benklop/screen-adapter/adapter/impedance.png

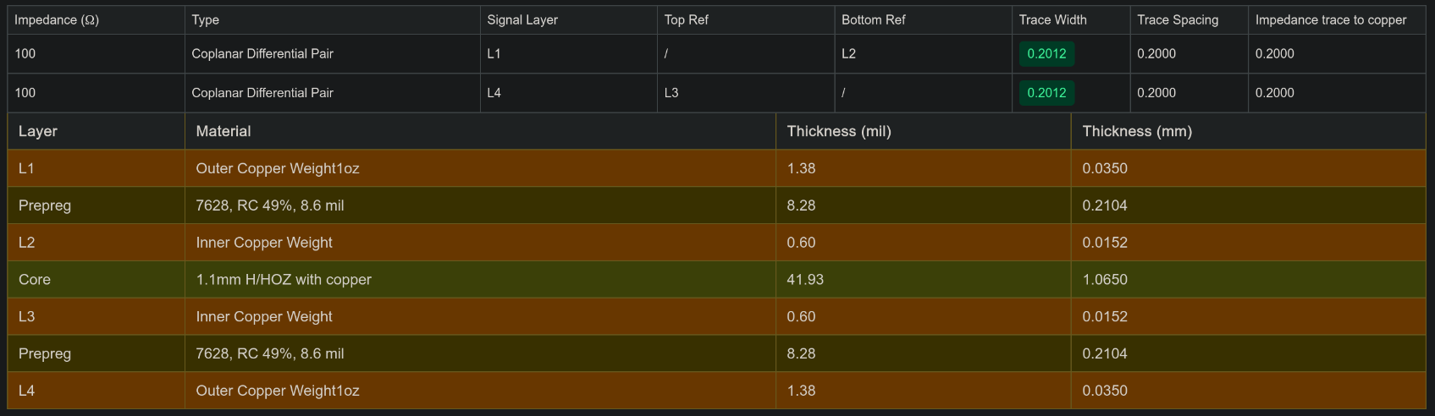
adapter/impedance.png
